0Zane/Nomad/assets/environment.png

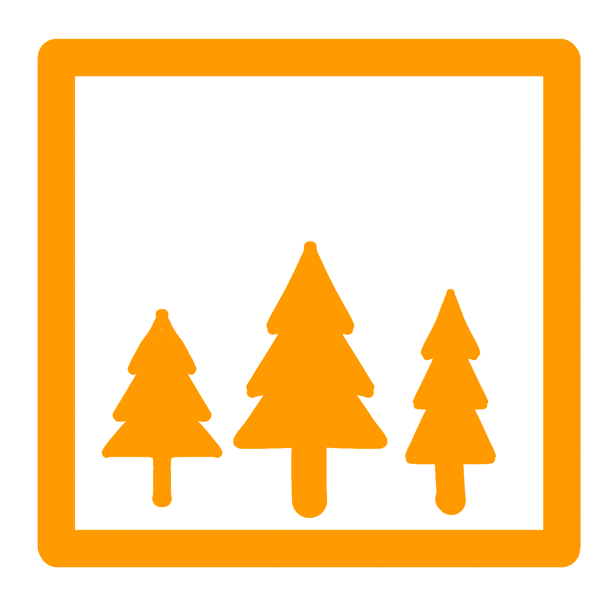
assets/environment.png
