0Zane/Nomad/assets/leftarrow.png

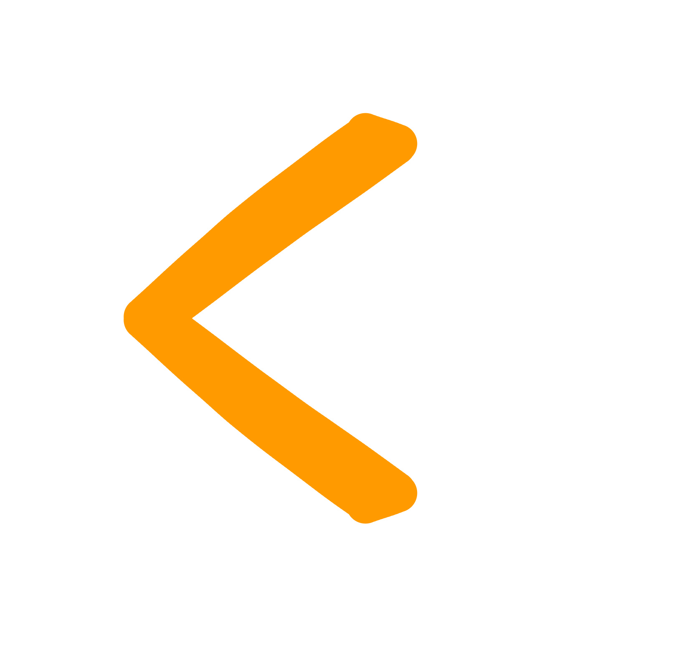
assets/leftarrow.png
