0Zane/Nomad/firmware/include/pins.h

//I2C BUS (Temperature sensor & GPIO extender)
#define TEMP_SCL 9
#define TEMP_SDA 8


//GPS MODULE
#define RXD2 16
#define TXD2 17


//GPIO EXENDER
#define INT 2


//FLASHLIGHT
#define FLASHLIGHT 1

//lORA MODULE
#define AUX 18
#define LORA_TX 21
#define LORA_RX 47
#define M1 48
#define M0 38
